rodan/tracy/firmware/drivers/nmea_parse.h

#ifndef __NMEA_PARSE_H__
#define __NMEA_PARSE_H__

#include <inttypes.h>

struct nmea_gprmc_t {
    uint8_t hour;
    uint8_t minute;
    uint8_t second;
    uint8_t lat_deg;
    uint8_t lat_min;
    uint16_t lat_fr;
    uint8_t lat_suffix;
    uint8_t lon_deg;
    uint8_t lon_min;
    uint16_t lon_fr;
    uint8_t lon_suffix;
    uint16_t speed;
    uint16_t heading;
    uint8_t day;
    uint8_t month;
    uint16_t year;
    uint8_t fix;
    uint32_t fixtime;
};

struct nmea_gprmc_t mc_f;
struct nmea_gprmc_t mc_t;

#ifdef CONFIG_GEOFENCE
struct geofence_t {
    double lat_home;
    double lon_home;
    double lat_cur;
    double lon_cur;
    double distance;
};

struct geofence_t geo;
#endif

uint8_t nmea_parse(char *str, const uint8_t len);
uint8_t str_to_uint32(char *str, uint32_t * out, const uint8_t seek,
                      const uint8_t len, const uint32_t min, const uint32_t max);
uint8_t str_to_uint16(char *str, uint16_t * out, const uint8_t seek,
                      const uint8_t len, const uint16_t min, const uint16_t max);

void haversine_km(struct geofence_t geofence);

#endif
